cnlohr/esp8266lighthouse/firmware/user/custom_commands.c

//Copyright 2015 <>< Charles Lohr, see LICENSE file.

#include <commonservices.h>
#include <esp82xxutil.h>
#include "lighthouse_decode.h"
#include <string.h>

extern remot_info premot_udp;

void ICACHE_FLASH_ATTR ReinitSettings()
{
}

void ICACHE_FLASH_ATTR SettingsLoaded()
{
}


int ICACHE_FLASH_ATTR CustomCommand(char * buffer, int retsize, char *pusrdata, unsigned short len)
{
	char * buffend = buffer;

	switch( pusrdata[1] )
	{
	case 'C': case 'c': //Custom command test
	{
		buffend += ets_sprintf( buffend, "CC" );
		return buffend-buffer;
	}
	case 'E': case 'e': //Get edges (does not advance packet)
	{
		buffend += ets_sprintf( buffend, "CE\t%d\t%d",LHSM.debugbufferflag,LHSM.edgecount );
		if( LHSM.debugbufferflag == 2 )
		{
			buffend+= ets_sprintf( buffend, "\t" );
			int k;

			struct LightEvent * dle = &LHSM.dhle;  //false-type casting
			ets_memcpy( buffend, dle, sizeof( struct LightEvent ) );
			buffend += sizeof( struct LightEvent );

			int tsend = LHSM.edgecount;
			if( tsend > 300 ) tsend = 300;
			//ets_memcpy( buffend, lighthousebuffer, tsend );
			for( k = 0; k < tsend; k++ )
			{
				uint32_t r = LHSM.edgetimesbase[k];
				*(buffend++) = r>>24;
				*(buffend++) = r>>16;
				*(buffend++) = r>>8;
				*(buffend++) = r;
			}
		}
		return buffend - buffer;
	}
	case 'P': case 'p': //Get last packet (advances packet)
	{
		LHSM.debugmonitoring = 1;
		buffend += ets_sprintf( buffend, "CP\t%d\t%d",LHSM.debugbufferflag,LHSM.debugbufferlen );
		if( LHSM.debugbufferflag == 2 )
		{
			int k;
			buffend+= ets_sprintf( buffend, "\t" );
			int tsend = LHSM.debugbufferlen;
			if( tsend > 300 ) tsend = 300;
			//ets_memcpy( buffend, lighthousebuffer, tsend );
			for( k = 0; k < tsend; k++ )
			{
				uint32_t r = LHSM.debugbufferbase[k];
				*(buffend++) = r>>24;
				*(buffend++) = r>>16;
				*(buffend++) = r>>8;
				*(buffend++) = r;
			}
			LHSM.debugbufferflag = 0;
		}
		return buffend-buffer;
	}
	}
	return -1;
}
